calcpsu/cptipb1a/cptibp1a-pcb/cptibp1a-pcb.asc

C1: cap; 47µ
C2: cap; 1µ
C3: cap; 4400µ
D1: diode; 1N4148
D2: diode; 1N4148
D3: diode; 1N4148
D4: diode; 1N4148
D5: schottky; 1N5817
D6: zener; UMZ5_1N
D7: diode; max40203
R1: res; 4.7
R2: res; 20
R3: res; 100
V1: voltage; sine(0 7 50)
V2: voltage; 4.2
X1: jumper
X2: jumper
X3: jumper
Named nets: 0, vin, bat_p, bat_n, calc, vcc
.tran 0 10 9.9
.model max40203 D(Ron=0.1 Roff=10Meg Vfwd=0.05 Vrev=6.5)
