calcpsu/cptipb1a/sim/calctibp1a.asc

C1: cap; 2200µ
C2: cap; 1µ
C3: cap; 1µ
D1: diode; 1N4148
D2: diode; 1N4148
D3: diode; 1N4148
D4: diode; 1N4148
D6: zener; UMZ5_1N
M1: pmos; AO6407
R1: res; 4.7
R2: res; 6
R3: res; 0.5
R4: res; 80
R5: res; 560k
R6: res; 220k
R7: res; 100k
U2: LTC1540
V1: voltage; SINE(0 7 50)
Named nets: 0, vp, vn, vcc, g
.tran 0 1 0.95
