calcpsu/cptipb1a/sim/Draft2.asc

M2: pmos; AO6407
R1: res; 1000k
R2: res; 10k
R3: res; 100k
R4: res; 100k
U1: LT6703-2
V1: voltage; PWL(0 0 0.5 6 1 0)
Named nets: vcc, vs, g, 0
.tran 1
